snietfeld/OpenChronograph/MainBoards/oc_1/fw/oc_1_default/src/timeval.cpp

#include "timeval.h"

int timeval_subtract (Timeval *result, Timeval *x, Timeval *y_in) {
  Timeval y = *y_in;

  /* Perform the carry for the later subtraction by updating y. */
  if (x->tv_usec < y.tv_usec) {
    int nsec = (y.tv_usec - x->tv_usec) / 1000000 + 1;
    y.tv_usec -= 1000000 * nsec;
    y.tv_sec += nsec;
  }
  if (x->tv_usec - y.tv_usec > 1000000) {
    int nsec = (x->tv_usec - y.tv_usec) / 1000000;
    y.tv_usec += 1000000 * nsec;
    y.tv_sec -= nsec;
  }

  /* Compute the time remaining to wait.
     tv_usec is certainly positive. */
  result->tv_sec = x->tv_sec - y.tv_sec;
  result->tv_usec = x->tv_usec - y.tv_usec;

  /* Return 1 if result is negative. */
  return x->tv_sec < y.tv_sec;
}
